ArduinoGelistirmePlatformu/esProg/Updater/EspFlasherTool/esProgSpiffs.PNG

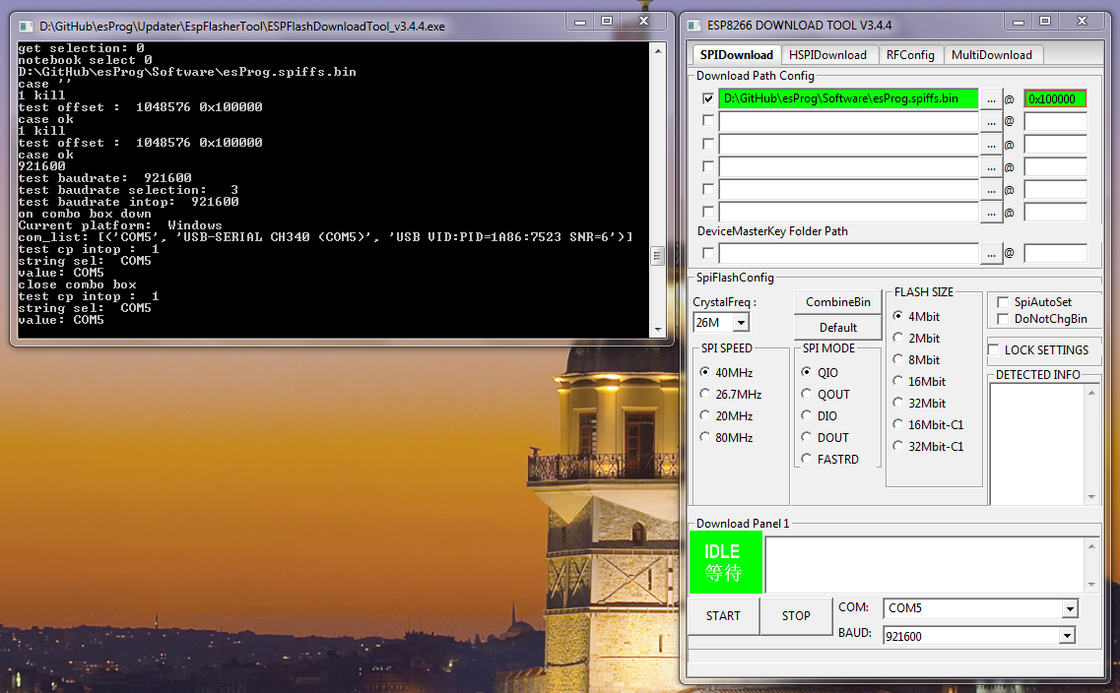
Updater/EspFlasherTool/esProgSpiffs.PNG
