ArduinoGelistirmePlatformu/esProg/Updater/EspFlasher/esProg Update 1.PNG

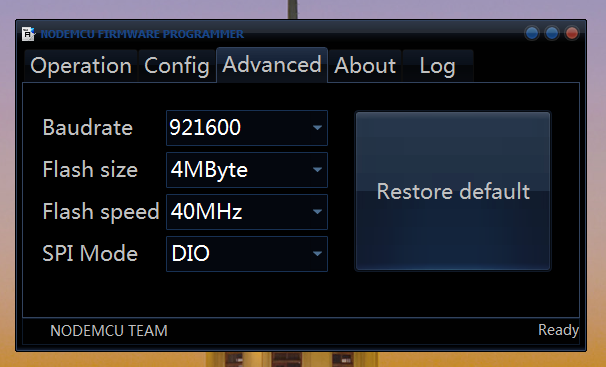
Updater/EspFlasher/esProg Update 1.PNG
