ArduinoGelistirmePlatformu/esProg/Updater/EspFlasher/esProg Update 3.PNG

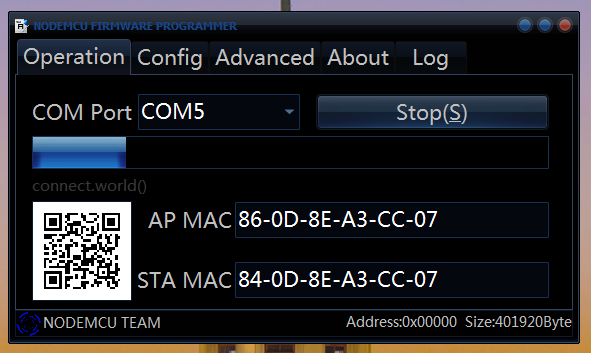
Updater/EspFlasher/esProg Update 3.PNG
